Mathesar/a500-sd-plus-controller/rtl/68k_bus_sync.v

// Copyright 2025 Dennis van Weeren
//
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

// CIA bus synchronizer
module sync_cia_bus (
    input       clk,                // destination clock
    input       _reset,             // reset
    output      rst,
    input       reg_decode,         // register address strobe
    output      reg_decode_synced,
    input       r_w,                // R/_W
    output      r_w_synced,
    input       _cs,                // chip select
    output      _cs_synced,
    input       e,                  // E clock
    output      e_synced,
    input       [7:0]data,          // databus
    output      [7:0]data_synced      
    );
    
    genvar i;		 
    reg [1:0]rst_ff;
    
    // reset signal
    always @(posedge clk or negedge _reset)
    begin
        if(!_reset)
            rst_ff[1:0] <= 2'b11; // async assert
        else 
            rst_ff[1:0] <= { rst_ff[0], 1'b0 }; // sync de-assert
    end
    
    // generate local reset
    `ifdef ALTERA_RESERVED_QIS   	 
        global CLK_BUF (
            .in             (rst_ff[1]), 
            .out            (rst)
        ); 
    `else
        assign rst = rst_ff[1];
    `endif
    
    // register decode
    sync SYNC_RS ( clk, reg_decode, reg_decode_synced );
    
    // r/_w
    sync SYNC_RW ( clk, r_w, r_w_synced );

    // chip select
    sync SYNC_CS ( clk, _cs, _cs_synced );

    // E clock
    sync SYNC_E ( clk, e, e_synced );
	
    // data bus
    generate
        for (i = 0; i <= 7; i = i + 1) 
        begin : gen_data
            sync SYNC_DATA (clk, data[i], data_synced[i]); 
        end
	endgenerate	

endmodule


// synchronizer
module sync (
    input       clk,            // clock to synchronize to
    input       in,             // asynchronous input
    output      out             // synchronized output
    );
    
    reg [1:0]ff;
    
    always @(posedge clk)
        ff[1:0] <= {ff[0], in};
        
    assign out = ff[1];
    
endmodule
